gwaves/duduclock/src/task.cpp

#include <TaskScheduler.h>
#include "tftUtil.h"
#include "net.h"
#include "common.h"
#include <dht11.h> //temp sensor

dht11 DHT;
#define DHT11_PIN 6  

enum CurrentPage currentPage = SETTING;
String scrollText[5]; // 轮播天气的信息
int currentIndex = 0; // 轮播索引
int currnetImgAnimIndex = 0; // 太空人动画索引
int tipsIndex = 0; // 获取数据时，动态文字的索引
volatile bool gTipsNeedUpdate = false; // 定时器中断标志，提示需要更新
NowWeather nowWeather; // 记录查询到的实况天气数据
FutureWeather futureWeather; // 记录查询到的七日天气数据
unsigned int timerCount = 0; // 计数器的值(ms)
bool isScrolling = false; // 轮播文字动画是否进行中
int scrollAnimPos = 0; // 轮播文字动画当前位置
String scrollAnimText = ""; // 当前轮播的文字

void drawWeatherContent();
void drawFutureWeatherPage();
void doScrollTextData(String win, int air, String text, String feelsLike, String vis);
void drawWeaImage(int icon);
void drawFutureWeaImage(int wea_img, int x, int y);
void drawCityAir(String city,int air);
void drawTHProgressBar(int temperature, int humidity);
void drawDateWeek();
void drawTitle();
void drawNumsByCount(unsigned int count);
String getWea(int icon);
String week(int tm_wday);
String monthDay(int tm_mon, int tm_mday);
void doHourMinuteSecond(int hour,int minute,int second,int *hourH,int *hourL,int *minuteH,int *minuteL,int *secondH,int *secondL);


//////////////////////////////// 多任务区域/////////////////////////////
void tAnimCallback();
void tScrollTextCallback();
void tScrollAnimCallback();
void tQueryWeatherCallback();
void tQueryFutureWeatherCallback();
void tCheckWiFiCallback();
void tCheckTimeCallback();
void tGetLocalTempCallback();
Scheduler runner;
Task tAnim(30, TASK_FOREVER, &tAnimCallback, &runner, true); // 30毫秒播放一帧太空人动画
Task tScrollText(5000, TASK_FOREVER, &tScrollTextCallback, &runner, true); // 5秒触发一次轮播
Task tScrollAnim(30, TASK_FOREVER, &tScrollAnimCallback, &runner, false); // 30毫秒滚动一帧文字
Task tQueryWeather(8*60 * 60 * 1000, TASK_FOREVER, &tQueryWeatherCallback, &runner, false); // 8x60分钟查询一次实况天气情况
Task tQueryFutureWeather(24*60 * 60 * 1000, TASK_FOREVER, &tQueryFutureWeatherCallback, &runner, false); // 24小时查询一次一周天气情况
Task tCheckWiFi(5 * 60 * 1000, TASK_FOREVER, &tCheckWiFiCallback, &runner, true); // 5分钟检查一次网络状态
Task tCheckTime(58 * 60 * 1000, TASK_FOREVER, &tCheckTimeCallback, &runner, true); // 58分钟进行一次NTP对时
Task tGetLocalTemp(30*1000,TASK_FOREVER,&tGetLocalTempCallback,&runner,true); //每隔30秒读一次本地温湿度
// 启动runner
void startRunner(){
  runner.startNow();
}
// 执行runner
void executeRunner(){
  runner.execute();
}
// 切换到非实况天气页面时，失能太空人动画和轮播天气情况的线程
void disableAnimScrollText(){
  tAnim.disable();
  tScrollText.disable();
}
// 切换回实况天气页面时，再开启太空人动画和轮播天气情况的线程
void enableAnimScrollText(){
  tAnim.enable();
  tScrollText.enable();
}
////////////////////////////////////////////////////////////////////////


//////////////// 定时器相关区域//////////////////////////////////////////
// 定义定时器
hw_timer_t *timerQueryWeather = NULL;
hw_timer_t *timerShowTips = NULL;
void IRAM_ATTR onTimerQueryWeather() {
  // 使能查询天气的多线程任务
  tQueryWeather.enable();
  tQueryFutureWeather.enable();
} 
void IRAM_ATTR onTimerShowTips() {
  // 中断中只做最小操作，UI绘制移到主循环
  tipsIndex++;
  if(tipsIndex == 6){
    tipsIndex = 0;
  }
  gTipsNeedUpdate = true;
}

// 在主循环或轮询中调用，实际执行UI绘制
void drawTipsIfNeeded(){
  if(!gTipsNeedUpdate) return;
  gTipsNeedUpdate = false;
  if(tipsIndex == 0){
    draw2LineText("同步天气数据",".");
  }else if(tipsIndex == 1){
    draw2LineText("同步天气数据","..");
  }else if(tipsIndex == 2){
    draw2LineText("同步天气数据","...");
  }else if(tipsIndex == 3){
    draw2LineText("同步天气数据","....");
  }else if(tipsIndex == 4){
    draw2LineText("同步天气数据",".....");
  }else if(tipsIndex == 5){
    draw2LineText("同步天气数据","......");
  }
}
// 初始化定时器，让查询天气的多线程任务在一小时后再使能
void startTimerQueryWeather(){
  timerQueryWeather = timerBegin(0, 80, true);// 1us计数一次
  timerAttachInterrupt(timerQueryWeather, &onTimerQueryWeather, false);
  timerAlarmWrite(timerQueryWeather, 3600000000, false); // 执行完一次后就取消这个定时器 (3600000000)3600秒，即60分钟后使能
  timerAlarmEnable(timerQueryWeather); 
}
// 初始化定时器，在获取初始数据时，给用户提示
void startTimerShowTips(){
  timerShowTips = timerBegin(1, 80, true);// 1us计数一次
  timerAttachInterrupt(timerShowTips, &onTimerShowTips, false); 
  timerAlarmWrite(timerShowTips, 1000000, true); // 每秒执行一次
  timerAlarmEnable(timerShowTips); 
}
///////////////////////////////////////////////////////////////////////


/////////// 绘制整个页面区域////////////////////////////////////////////
// 绘制一周天气页面
void drawFutureWeatherPage(){
  reflashTFT(); // 清空屏幕
  // 绘制标题
  clk.createSprite(240, 60);
  clk.loadFont(clock_other_title_35);
  clk.setTextDatum(CC_DATUM);
  clk.setTextColor(penColor);
  clk.fillSprite(backFillColor);  
  clk.drawString("6日天气预报",120,30);
  clk.drawFastHLine(0,56,240,penColor);
  clk.drawFastHLine(0,58,240,penColor);
  clk.pushSprite(0,0);
  clk.deleteSprite();
  // 绘制天气图案
  drawFutureWeaImage(futureWeather.day1wea_img, 15, 65);
  drawFutureWeaImage(futureWeather.day2wea_img, 95, 65);
  drawFutureWeaImage(futureWeather.day3wea_img, 175, 65);
  drawFutureWeaImage(futureWeather.day4wea_img, 15, 195);
  drawFutureWeaImage(futureWeather.day5wea_img, 95, 195);
  drawFutureWeaImage(futureWeather.day6wea_img, 175, 195);
  // 绘制上部分文字
  clk.loadFont(clock_future_weather_20);
  clk.setTextDatum(CC_DATUM);
  clk.createSprite(240, 70);
  clk.setTextColor(penColor);
  clk.fillSprite(backFillColor);
  clk.drawString(futureWeather.day1date.substring(5),40,10);
  clk.drawString(futureWeather.day1wea,40,35);
  clk.drawString(String(futureWeather.day1tem_night) + "-" + String(futureWeather.day1tem_day) + "℃",40,60);
  clk.drawString(futureWeather.day2date.substring(5),120,10);
  clk.drawString(futureWeather.day2wea,120,35);
  clk.drawString(String(futureWeather.day2tem_night) + "-" + String(futureWeather.day2tem_day) + "℃",120,60);
  clk.drawString(futureWeather.day3date.substring(5),200,10);
  clk.drawString(futureWeather.day3wea,200,35);
  clk.drawString(String(futureWeather.day3tem_night) + "-" + String(futureWeather.day3tem_day) + "℃",200,60);
  clk.pushSprite(0,115);
  clk.deleteSprite();
  // 绘制下部分文字
  clk.createSprite(240, 70);
  clk.setTextColor(penColor);
  clk.fillSprite(backFillColor);
  clk.drawString(futureWeather.day4date.substring(5),40,10);
  clk.drawString(futureWeather.day4wea,40,35);
  clk.drawString(String(futureWeather.day4tem_night) + "-" + String(futureWeather.day4tem_day) + "℃",40,60);
  clk.drawString(futureWeather.day5date.substring(5),120,10);
  clk.drawString(futureWeather.day5wea,120,35);
  clk.drawString(String(futureWeather.day5tem_night) + "-" + String(futureWeather.day5tem_day) + "℃",120,60);
  clk.drawString(futureWeather.day6date.substring(5),200,10);
  clk.drawString(futureWeather.day6wea,200,35);
  clk.drawString(String(futureWeather.day6tem_night) + "-" + String(futureWeather.day6tem_day) + "℃",200,60);
  clk.pushSprite(0,245);
  clk.deleteSprite();
  clk.unloadFont();
}
// 绘制空气质量页面
void drawAirPage(){
  reflashTFT(); // 清空屏幕
  clk.loadFont(air_24);
  // 绘制标题
  clk.createSprite(240, 50);
  clk.fillSprite(backFillColor);
  clk.setTextDatum(CC_DATUM);
  clk.setTextColor(penColor);
  clk.drawString("空气质量指数",120,25);
  clk.pushSprite(0,0);
  clk.deleteSprite();
  // 绘制六种污染物
  clk.setTextDatum(ML_DATUM);
  clk.setTextColor(TFT_WHITE);
  // pm10 颗粒物
  clk.createSprite(236, 43);
  clk.fillSprite(backFillColor);
  clk.fillRoundRect(0,0,236,43,7,TFT_DARKGREY);
  clk.drawString("颗粒物",10,23);
  clk.drawString("PM10",110,23);
  clk.drawString(nowWeather.pm10,185,23);
  clk.pushSprite(2,50);
  clk.deleteSprite();
  // pm2p5 颗粒物
  clk.createSprite(236, 43);
  clk.fillSprite(backFillColor);
  clk.fillRoundRect(0,0,236,43,7,0x2C3E);
  clk.drawString("颗粒物",10,23);
  clk.drawString("PM2.5",110,23);
  clk.drawString(nowWeather.pm2p5,185,23);
  clk.pushSprite(2,95);
  clk.deleteSprite();
  // no2  二氧化氮
  clk.createSprite(236, 43);
  clk.fillSprite(backFillColor);
  clk.fillRoundRect(0,0,236,43,7,0x0E27);
  clk.drawString("二氧化氮",10,23);
  clk.drawString("NO2",110,23);
  clk.drawString(nowWeather.no2,185,23);
  clk.pushSprite(2,140);
  clk.deleteSprite();
  // so2  二氧化硫
  clk.createSprite(236, 43);
  clk.fillSprite(backFillColor);
  clk.fillRoundRect(0,0,236,43,7,TFT_GOLD);
  clk.drawString("二氧化硫",10,23);
  clk.drawString("SO2",110,23);
  clk.drawString(nowWeather.so2,185,23);
  clk.pushSprite(2,185);
  clk.deleteSprite();
  // co  一氧化碳
  clk.createSprite(236, 43);
  clk.fillSprite(backFillColor);
  clk.fillRoundRect(0,0,236,43,7,TFT_ORANGE);
  clk.drawString("一氧化碳",10,23);
  clk.drawString("CO",110,23);
  clk.drawString(nowWeather.co,185,23);
  clk.pushSprite(2,230);
  clk.deleteSprite();
  // o3  臭氧
  clk.createSprite(236, 43);
  clk.fillSprite(backFillColor);
  clk.fillRoundRect(0,0,236,43,7,TFT_RED);
  clk.drawString("臭氧",10,23);
  clk.drawString("O3",110,23);
  clk.drawString(nowWeather.o3,185,23);
  clk.pushSprite(2,275);
  clk.deleteSprite();
  clk.unloadFont();
}
// 绘制实况天气页面
void drawWeatherPage(){
  //清空屏幕
  reflashTFT();
  //绘制标题
  drawTitle();
  //绘制时间、日期、星期
  drawDateWeek();
  //绘制温湿度图标
  if(backColor == BACK_BLACK){
    tft.pushImage(7,235,40,40,temperature_black);
    tft.pushImage(5,275,40,40,humidity_black);
  }else{
    tft.pushImage(7,235,40,40,temperature);
    tft.pushImage(5,275,40,40,humidity);
  } 
  // 绘制天气相关内容
  drawWeatherContent();
}
// 绘制计时器页面
void drawTimerPage(){
  //清空屏幕
  reflashTFT();
  //绘制标题
  clk.createSprite(240, 60);
  clk.loadFont(clock_other_title_35);
  clk.setTextDatum(CC_DATUM);
  clk.setTextColor(penColor);
  clk.fillSprite(backFillColor);  
  clk.drawString("计时器",120,30);
  clk.drawFastHLine(0,56,240,penColor);
  clk.drawFastHLine(0,58,240,penColor);
  clk.pushSprite(0,0);
  clk.deleteSprite();
  //显示提示文字
  clk.setColorDepth(8);
  clk.setTextDatum(CC_DATUM);
  clk.loadFont(clock_timer_24);
  clk.createSprite(240, 60);
  clk.setTextColor(penColor);
  clk.fillSprite(backFillColor);
  clk.drawString("单击开启/停止计时",120,45);
  clk.drawString("长按3秒计数器归零",120,15);
  clk.pushSprite(0,250);
  clk.deleteSprite();
  clk.unloadFont(); 
  //根据计数器当前的数值进行绘制
  drawNumsByCount(timerCount);
}

// 绘制出厂设置页面
void drawResetPage(){
  //清空屏幕
  reflashTFT();
  // 绘制标题
  clk.createSprite(240, 60);
  clk.loadFont(clock_other_title_35);
  clk.setTextDatum(CC_DATUM);
  clk.setTextColor(penColor);
  clk.fillSprite(backFillColor);  
  clk.drawString("还原设置",120,30);
  clk.drawFastHLine(0,56,240,penColor);
  clk.drawFastHLine(0,58,240,penColor);
  clk.pushSprite(0,0);
  clk.deleteSprite();
  // 绘制提示文字
  clk.createSprite(240, 260);
  clk.loadFont(clock_tips_28);
  clk.setTextDatum(CC_DATUM);
  clk.setTextColor(penColor);
  clk.fillSprite(backFillColor);  
  clk.drawString("长按3秒钟",120,90);
  clk.drawString("恢复出厂设置",120,140);
  clk.pushSprite(0,60);
  clk.deleteSprite();
}
// 绘制主题设置页面
void drawThemePage(){
  // 清空屏幕
  reflashTFT();
  // 绘制标题
  clk.createSprite(240, 60);
  clk.loadFont(clock_other_title_35);
  clk.setTextDatum(CC_DATUM);
  clk.setTextColor(penColor);
  clk.fillSprite(backFillColor);
  clk.drawString("主题切换",120,30);
  clk.drawFastHLine(0,56,240,penColor);
  clk.drawFastHLine(0,58,240,penColor);
  clk.pushSprite(0,0);
  clk.deleteSprite();
  // 绘制提示文字
  clk.createSprite(240, 260);
  clk.loadFont(clock_tips_28);
  clk.setTextDatum(CC_DATUM);
  clk.setTextColor(penColor);
  clk.fillSprite(backFillColor);  
  clk.drawString("长按3秒钟",120,90);
  if(backColor == BACK_BLACK){
    clk.drawString("切换白色主题",120,140);
  }else{
    clk.drawString("切换黑色主题",120,140);
  }
  clk.pushSprite(0,60);
  clk.deleteSprite();
}
/////////////////////////////////////////////////////////////////////


/////////// 多任务协程回调区域 ////////////////////////////////////////
// NTP对时
void tCheckTimeCallback(){
  getNTPTime();
}
// 检查Wifi状态,如果失败，重新连接
void tCheckWiFiCallback(){
  log_i("开始检查网络状态");
  checkWiFiStatus();
}
// 绘制太空人任务
void tAnimCallback(){
  int x=170, y=240 , w=70;
  if(backColor == BACK_BLACK){
    switch(currnetImgAnimIndex){
      case 0:
        tft.pushImage(x, y, w, w,yuhangyuan0_black);
        break;
      case 1:
        tft.pushImage(x, y, w, w,yuhangyuan1_black);
        break;
      case 2:
        tft.pushImage(x, y, w, w,yuhangyuan2_black);
        break;
      case 3:
        tft.pushImage(x, y, w, w,yuhangyuan3_black);
        break;
      case 4:
        tft.pushImage(x, y, w, w,yuhangyuan4_black);
        break;
      case 5:
        tft.pushImage(x, y, w, w,yuhangyuan5_black);
        break;
      case 6:
        tft.pushImage(x, y, w, w,yuhangyuan6_black);
        break;
      case 7:
        tft.pushImage(x, y, w, w,yuhangyuan7_black);
        break;
      case 8:
        tft.pushImage(x, y, w, w,yuhangyuan8_black);
        break;
      case 9:
        tft.pushImage(x, y, w, w,yuhangyuan9_black);
        break;
      default:
        currnetImgAnimIndex = 9;
        break;
    }
  }else{
    switch(currnetImgAnimIndex){
      case 0:
        tft.pushImage(x, y, w, w,yuhangyuan0);
        break;
      case 1:
        tft.pushImage(x, y, w, w,yuhangyuan1);
        break;
      case 2:
        tft.pushImage(x, y, w, w,yuhangyuan2);
        break;
      case 3:
        tft.pushImage(x, y, w, w,yuhangyuan3);
        break;
      case 4:
        tft.pushImage(x, y, w, w,yuhangyuan4);
        break;
      case 5:
        tft.pushImage(x, y, w, w,yuhangyuan5);
        break;
      case 6:
        tft.pushImage(x, y, w, w,yuhangyuan6);
        break;
      case 7:
        tft.pushImage(x, y, w, w,yuhangyuan7);
        break;
      case 8:
        tft.pushImage(x, y, w, w,yuhangyuan8);
        break;
      case 9:
        tft.pushImage(x, y, w, w,yuhangyuan9);
        break;
      default:
        currnetImgAnimIndex = 9;
        break;
    }
  }
  currnetImgAnimIndex += 1;
  if(currnetImgAnimIndex == 10){
    currnetImgAnimIndex = 0;
  } 
}
// 轮播ScrollText任务（触发器，每5秒启动一次动画）
void tScrollTextCallback(){
  if(!isScrolling && scrollText[currentIndex]){
    isScrolling = true;
    scrollAnimPos = 24;
    scrollAnimText = scrollText[currentIndex];
    tScrollAnim.enable();
  }
}

// 轮播文字逐帧动画
void tScrollAnimCallback(){
  if(!isScrolling) return;

  clk.setColorDepth(8);
  clk.loadFont(city_wea_24);
  clk.createSprite(160, 24);
  clk.setTextColor(penColor);
  clk.fillSprite(backFillColor);
  clk.setTextDatum(CC_DATUM);
  clk.drawString(scrollAnimText, 80, scrollAnimPos + 12);
  clk.pushSprite(5, 102);
  clk.deleteSprite();
  clk.unloadFont();

  scrollAnimPos--;
  if(scrollAnimPos <= 0){
    isScrolling = false;
    tScrollAnim.disable();
    if(currentIndex >= 4){
      currentIndex = 0;
    }else{
      currentIndex++;
    }
  }
}
// 查询天气和空气质量
void tQueryWeatherCallback(){
  getNowWeather();
  getAir();
  if(queryNowWeatherSuccess || queryAirSuccess){
    Serial.println("更新实时天气信息");
    // 如果是在实况天气页面，则绘制天气相关内容
    if(currentPage == WEATHER){
      drawWeatherContent();
    }
  }
}
// 查询未来天气
void tQueryFutureWeatherCallback(){
  getFutureWeather();
  if(queryFutureWeatherSuccess){ // 查询一周天气成功，再继续下面的操作
    Serial.println("更新一周天气信息");
    // 如果是在一周天气页面，则绘制一周天气相关内容
    if(currentPage == FUTUREWEATHER){
      drawFutureWeatherPage();
    }
  }
}
/////////////////////////////////////////////////////////////////////


// 根据计数器当前的数值进行绘制
void drawNumsByCount(unsigned int count){
  clk.setColorDepth(8);
  clk.setTextDatum(CC_DATUM);
  clk.createSprite(240, 180);
  clk.setTextColor(penColor);
  clk.fillSprite(backFillColor);
  // 根据 count 计数器的毫秒值，计算对应的小时、分、秒、毫秒 
  int hour = count / 1000 / 60 / 60;
  int minute = (count / 1000 / 60) % 60;
  int second = (count / 1000) % 60;
  int millisecond = count % 1000;
  clk.loadFont(clock_timer_hour_52);
  clk.setTextColor(penColor);
  clk.drawString(String(hour) + " H",120,50);
  clk.unloadFont(); 
  clk.loadFont(clock_num_big_64);
  clk.drawString(String(minute / 10),20,120);
  clk.drawString(String(minute % 10),55,120);
  clk.drawString(":",80,120);
  clk.setTextColor(0xFC60);
  clk.drawString(String(second / 10),110,120);
  clk.drawString(String(second % 10),145,120);
  clk.unloadFont();
  clk.loadFont(clock_num_50);
  clk.setTextColor(TFT_RED);
  clk.drawString(String((millisecond / 10) / 10),187,123);
  clk.drawString(String((millisecond / 10) % 10),215,123);
  clk.unloadFont();
  // Serial.print(String(millisecond));Serial.println("毫秒");
  // Serial.print(String(second));Serial.println("秒");
  // Serial.print(String(minute));Serial.println("分");
  // Serial.print(String(hour));Serial.println("时");
  clk.pushSprite(0,70);
  clk.deleteSprite();
}
// 绘制天气相关内容
void drawWeatherContent(){
  //绘制温湿度条（内部已处理清屏，避免数字变化残影）
  drawTHProgressBar(nowWeather.temp,nowWeather.humidity);
  //绘制城市、空气质量
  drawCityAir(city,nowWeather.air);
  //绘制天气图案和文字
  drawWeaImage(nowWeather.icon);
  //处理轮播字条数据(风向win,空气指数air,天气实况text,体感温度feelsLike,能见度vis)
  doScrollTextData(nowWeather.win, nowWeather.air, nowWeather.text, nowWeather.feelsLike, nowWeather.vis);
}
//处理轮播字条数据(风向win,空气指数air,天气实况text,体感温度feelsLike,能见度vis)
void doScrollTextData(String win, int air, String text, String feelsLike, String vis){
  scrollText[0] = "";
  scrollText[1] = "";
  scrollText[2] = "";
  scrollText[3] = "";
  scrollText[4] = "";
  scrollText[0] = "今日" + text;
  scrollText[1] = win;
  scrollText[2] = feelsLike;
  scrollText[3] = vis;
  scrollText[4] += "空气指数";
  scrollText[4] += air;
}
//绘制天气图案和文字
void drawWeaImage(int icon){
  String s = getWea(icon);
  if(backColor == BACK_BLACK){
    if(s.equals("雪")){
      tft.pushImage(180,55,50,50,xue_black);
    }else if(s.equals("雷")){
      tft.pushImage(180,55,50,50,lei_black);
    }else if(s.equals("沙尘")){
      tft.pushImage(180,55,50,50,shachen_black);
    }else if(s.equals("雾")){
      tft.pushImage(180,55,50,50,wu_black);
    }else if(s.equals("冰雹")){
      tft.pushImage(180,55,50,50,bingbao_black);
    }else if(s.equals("多云")){
      tft.pushImage(180,55,50,50,yun_black);
    }else if(s.equals("雨")){
      tft.pushImage(180,55,50,50,yu_black);
    }else if(s.equals("阴")){
      tft.pushImage(180,55,50,50,yin_black);
    }else if(s.equals("晴")){
      tft.pushImage(180,55,50,50,qing_black);
    }
  }else{
    if(s.equals("雪")){
      tft.pushImage(180,55,50,50,xue);
    }else if(s.equals("雷")){
      tft.pushImage(180,55,50,50,lei);
    }else if(s.equals("沙尘")){
      tft.pushImage(180,55,50,50,shachen);
    }else if(s.equals("雾")){
      tft.pushImage(180,55,50,50,wu);
    }else if(s.equals("冰雹")){
      tft.pushImage(180,55,50,50,bingbao);
    }else if(s.equals("多云")){
      tft.pushImage(180,55,50,50,yun);
    }else if(s.equals("雨")){
      tft.pushImage(180,55,50,50,yu);
    }else if(s.equals("阴")){
      tft.pushImage(180,55,50,50,yin);
    }else if(s.equals("晴")){
      tft.pushImage(180,55,50,50,qing);
    }
  }
  clk.setColorDepth(8);
  clk.setTextDatum(CC_DATUM);
  clk.loadFont(city_wea_24);
  clk.createSprite(60, 28);
  clk.fillSprite(backFillColor);
  clk.fillRoundRect(0,0,60,32,0,0x4208);// 进度条填充(x方向,y方向,长度,高度,圆角,颜色)
  clk.setTextColor(0xFFFF);
  clk.drawString(s,29,15);
  clk.pushSprite(172,120);
  clk.deleteSprite();
  clk.unloadFont(); 
}
//绘制一周天气图案
void drawFutureWeaImage(int wea_img, int x, int y){
  String s = getWea(wea_img);
  if(backColor == BACK_BLACK){
    if(s.equals("雪")){
      tft.pushImage(x,y,50,50,xue_black);
    }else if(s.equals("雷")){
      tft.pushImage(x,y,50,50,lei_black);
    }else if(s.equals("沙尘")){
      tft.pushImage(x,y,50,50,shachen_black);
    }else if(s.equals("雾")){
      tft.pushImage(x,y,50,50,wu_black);
    }else if(s.equals("冰雹")){
      tft.pushImage(x,y,50,50,bingbao_black);
    }else if(s.equals("多云")){
      tft.pushImage(x,y,50,50,yun_black);
    }else if(s.equals("雨")){
      tft.pushImage(x,y,50,50,yu_black);
    }else if(s.equals("阴")){
      tft.pushImage(x,y,50,50,yin_black);
    }else if(s.equals("晴")){
      tft.pushImage(x,y,50,50,qing_black);
    }
  }else{
    if(s.equals("雪")){
      tft.pushImage(x,y,50,50,xue);
    }else if(s.equals("雷")){
      tft.pushImage(x,y,50,50,lei);
    }else if(s.equals("沙尘")){
      tft.pushImage(x,y,50,50,shachen);
    }else if(s.equals("雾")){
      tft.pushImage(x,y,50,50,wu);
    }else if(s.equals("冰雹")){
      tft.pushImage(x,y,50,50,bingbao);
    }else if(s.equals("多云")){
      tft.pushImage(x,y,50,50,yun);
    }else if(s.equals("雨")){
      tft.pushImage(x,y,50,50,yu);
    }else if(s.equals("阴")){
      tft.pushImage(x,y,50,50,yin);
    }else if(s.equals("晴")){
      tft.pushImage(x,y,50,50,qing);
    }
  } 
}
//绘制城市、空气质量
void drawCityAir(String city,int air){
  clk.setColorDepth(8);
  clk.setTextDatum(CC_DATUM);
  //城市
  clk.loadFont(city_wea_24);
  clk.createSprite(100, 32);
  clk.fillSprite(backFillColor);
  clk.setTextColor(0xFC60);
  clk.drawString(city,50,17); 
  clk.pushSprite(0,60);
  clk.deleteSprite();
  clk.unloadFont();
  //空气质量， ≤50优（绿色），≤100良（蓝），≤150中（橙），≤200差（红）
  clk.loadFont(city_wea_24);
  String level;
  uint16_t color;
  if(air <= 50){
    color = 0x0E27;
    level = "优";
  }else if(air <= 100){
    color = 0x2C3E;
    level = "良";
  }else if(air <= 150){
    color = 0xFC60;
    level = "中";
  }else{
    color = TFT_RED;
    level = "差";
  }
  clk.createSprite(60, 32);
  clk.fillSprite(backFillColor);
  clk.fillRoundRect(0,0,60,32,7,color);// 进度条填充(x方向,y方向,长度,高度,圆角,颜色)
  clk.setTextColor(0xFFFF);
  clk.drawString(level,30,17);
  clk.pushSprite(105,60);
  clk.deleteSprite();
  clk.unloadFont();
}
// 绘制温湿度数据
void drawTHProgressBar(int temperature, int humidity){
  // 清除整个温湿度文字区域（左右两侧），防止数字位数或正负号变化时产生残影
  tft.fillRect(28, 238, 142, 58, backFillColor);
  tft.loadFont(city_wea_24);
  tft.setTextColor(penColor,backFillColor);
  if(temperature < 0){
    tft.drawNumber(temperature,115,245);
  }else{
    tft.drawNumber(temperature,127,245);
  }
  tft.drawString("℃",149,245);
  if(humidity >= 100){
    tft.drawNumber(humidity,115,285);
  }else{
    tft.drawNumber(humidity,127,285);
  }
  tft.drawString("%",157,285);

  //绘制室内温度信息
  tft.setTextColor(penColor,backFillColor);
  if(DHT.temperature < 0){
    tft.drawNumber(DHT.temperature,35,245);
  }else{
    tft.drawNumber(DHT.temperature,57,245);
  }
  tft.drawString("℃",79,245);
  if(DHT.humidity >= 100){
    tft.drawNumber(DHT.humidity,35,285);
  }else{
    tft.drawNumber(DHT.humidity,57,285);
  }
  tft.drawString("%",87,285);

  tft.unloadFont();
}
// 绘制时间、日期、星期
void drawDateWeek(){
  // 获取RTC时间
  struct tm timeinfo;
  if (!getLocalTime(&timeinfo)){
    Serial.println("获取RTC时间失败");
    return;
  }
  clk.setColorDepth(8);
  //中部时、分、秒
  int hourH,hourL,minuteH,minuteL,secondH,secondL;
  doHourMinuteSecond(timeinfo.tm_hour,timeinfo.tm_min,timeinfo.tm_sec,&hourH,&hourL,&minuteH,&minuteL,&secondH,&secondL);
  //时、分
  clk.createSprite(165, 60);
  clk.setTextColor(penColor);
  clk.fillSprite(backFillColor);
  clk.loadFont(clock_num_big_64);
  clk.setTextDatum(CC_DATUM);
  clk.drawNumber(hourH,20,32);
  clk.drawNumber(hourL,55,32);
  clk.drawString(":",80,32);
  clk.setTextColor(0xFC60);
  clk.drawNumber(minuteH,110,32);
  clk.drawNumber(minuteL,145,32);
  clk.unloadFont();
  clk.pushSprite(5,135);
  clk.deleteSprite();
  //秒
  clk.createSprite(55, 40);
  clk.fillSprite(backFillColor);
  clk.loadFont(clock_num_mid_35);
  clk.setTextDatum(CC_DATUM);
  clk.setTextColor(TFT_RED);
  clk.drawNumber(secondH,12,20);
  clk.drawNumber(secondL,32,20);
  clk.unloadFont();
  clk.pushSprite(180,155);
  clk.deleteSprite();
  //底部日期、星期
  clk.loadFont(city_wea_24);
  //星期
  clk.createSprite(58, 25);
  clk.setTextColor(penColor);
  clk.fillSprite(backFillColor);
  clk.setTextDatum(CC_DATUM);  
  clk.drawString(week(timeinfo.tm_wday),27,16);
  clk.pushSprite(123,202);
  clk.deleteSprite();
  //月日
  clk.createSprite(98, 25);
  clk.setTextColor(penColor);
  clk.fillSprite(backFillColor);
  clk.setTextDatum(CC_DATUM);
  clk.drawString(monthDay(timeinfo.tm_mon,timeinfo.tm_mday),49,16);
  clk.pushSprite(5,202);
  clk.deleteSprite();
  clk.unloadFont();
}
// 绘制标题
void drawTitle(){
  clk.createSprite(240, 51);
  clk.setTextColor(penColor);
  clk.fillSprite(backFillColor);
  //clk.loadFont(name_42);
  clk.loadFont(city_wea_24);
  clk.setTextDatum(CC_DATUM);
  //clk.drawString("Taotao Clock",120,35);
  clk.drawString("Make    KC    Great",120,35);
  clk.unloadFont();
  clk.drawFastHLine(0,48,240,penColor);
  clk.drawFastHLine(0,50,240,penColor);
  clk.pushSprite(0,0);
  clk.deleteSprite();
}
// 根据icon获得天气状况
String getWea(int icon){
  String s = "";
  switch (icon){
    case 100:
    case 150:
      s = "晴";
      break;
    case 104:
      s = "阴";
      break;
    case 300:
    case 301:
    case 305:
    case 306:
    case 307:
    case 308:
    case 309:
    case 310:
    case 311:
    case 312:
    case 313:
    case 314:
    case 315:
    case 316:
    case 317:
    case 318:
    case 350:
    case 351:
    case 399:
      s = "雨";
      break;
    case 101:
    case 102:
    case 103:
    case 151:
    case 152:
    case 153:
      s = "多云";
      break;
    case 304:
      s = "冰雹";
      break;
    case 500:
    case 501:
    case 502:
    case 509:
    case 510:
    case 511:
    case 512:
    case 513:
    case 514:
    case 515:
      s = "雾";
      break;
    case 503:
    case 504:
    case 507:
    case 508:
      s = "沙尘";
      break;
    case 302:
    case 303:
      s = "雷";
      break;
    case 400:
    case 401:
    case 402:
    case 403:
    case 404:
    case 405:
    case 406:
    case 407:
    case 408:
    case 409:
    case 410:
    case 456:
    case 457:
    case 499:
      s = "雪";
      break;
    default:
      s = "晴";
      break;  
  }
  return s;
}
//处理星期
String week(int tm_wday){
  String wk[7] = {"日","一","二","三","四","五","六"};
  String s = "周" + wk[tm_wday];
  return s;
}
//处理月日
String monthDay(int tm_mon, int tm_mday){
  String s = "";
  s = s + (tm_mon + 1);
  s = s + "月" + tm_mday + "日";
  return s;
}
//处理时分秒
void doHourMinuteSecond(int hour,int minute,int second,int *hourH,int *hourL,int *minuteH,int *minuteL,int *secondH,int *secondL){
  *hourH = hour / 10;
  *hourL = hour % 10;
  *minuteH = minute / 10;
  *minuteL = minute % 10;
  *secondH = second / 10;
  *secondL = second % 10;
}

void tGetLocalTempCallback()
{
  int chk;
  int errCnt=0;
  log_v("DHT11, \t");
  chk = DHT.read(DHT11_PIN);    // READ DATA
  while(chk != DHTLIB_OK && errCnt < 5){
    delay(100);
    chk = DHT.read(DHT11_PIN);    // READ DATA
    errCnt++;
  }
  switch (chk){
    case DHTLIB_OK:  
                log_v("OK,\t"); 
                break;
    case DHTLIB_ERROR_CHECKSUM: 
                log_e("DHT11 Checksum error"); 
                break;
    case DHTLIB_ERROR_TIMEOUT: 
                log_e("DHT11 Time out error"); 
                break;
    default: 
                log_e("DHT11 Unknown error"); 
                break;
  }
 // DISPLAT DATA
  log_v("%d \t %d",DHT.humidity,DHT.temperature);
  //只刷新温湿度区域，避免整屏闪烁
  if(currentPage == WEATHER){
    drawTHProgressBar(nowWeather.temp, nowWeather.humidity);
  }
}
