gwaves/duduclock/src/common.h

#ifndef __COMMON_H
#define __COMMON_H

#include <Arduino.h>
#include "img/yuhangyuan/yuhangyuan0_black.h"
#include "img/yuhangyuan/yuhangyuan1_black.h"
#include "img/yuhangyuan/yuhangyuan2_black.h"
#include "img/yuhangyuan/yuhangyuan3_black.h"
#include "img/yuhangyuan/yuhangyuan4_black.h"
#include "img/yuhangyuan/yuhangyuan5_black.h"
#include "img/yuhangyuan/yuhangyuan6_black.h"
#include "img/yuhangyuan/yuhangyuan7_black.h"
#include "img/yuhangyuan/yuhangyuan8_black.h"
#include "img/yuhangyuan/yuhangyuan9_black.h"
#include "img/yuhangyuan/yuhangyuan0.h"
#include "img/yuhangyuan/yuhangyuan1.h"
#include "img/yuhangyuan/yuhangyuan2.h"
#include "img/yuhangyuan/yuhangyuan3.h"
#include "img/yuhangyuan/yuhangyuan4.h"
#include "img/yuhangyuan/yuhangyuan5.h"
#include "img/yuhangyuan/yuhangyuan6.h"
#include "img/yuhangyuan/yuhangyuan7.h"
#include "img/yuhangyuan/yuhangyuan8.h"
#include "img/yuhangyuan/yuhangyuan9.h"
#include "img/wea/xue.h"
#include "img/wea/lei.h"
#include "img/wea/shachen.h"
#include "img/wea/wu.h"
#include "img/wea/bingbao.h"
#include "img/wea/yun.h"
#include "img/wea/yu.h"
#include "img/wea/yin.h"
#include "img/wea/qing.h"
#include "img/wea/xue_black.h"
#include "img/wea/lei_black.h"
#include "img/wea/shachen_black.h"
#include "img/wea/wu_black.h"
#include "img/wea/bingbao_black.h"
#include "img/wea/yun_black.h"
#include "img/wea/yu_black.h"
#include "img/wea/yin_black.h"
#include "img/wea/qing_black.h"
#include "img/temperature.h"
#include "img/humidity.h"
#include "img/temperature_black.h"
#include "img/humidity_black.h"
#include "img/QRcode.h"
#include "font/clock_num_big_64.h"
#include "font/clock_timer_hour_52.h"
#include "font/clock_num_mid_35.h"
#include "font/clock_num_50.h"
#include "font/city_wea_24.h"
#include "font/clock_tips_28.h"
#include "font/clock_timer_24.h"
#include "font/clock_future_weather_20.h"
#include "font/clock_other_title_35.h"
//#include "font/clock_title_45.h"
#include "font/air_24.h"
//#include "font/taotao_45.h"
#include "font/name_42.h"
#define NTP3 "ntp5.ntsc.ac.cn"
#define NTP2 "ntp5.ict.ac.cn"
#define NTP1 "ntp5.aliyun.com"
#define BACK_BLACK 0
#define BACK_WHITE 1
#define D4 12  // 开发板D4灯
#define BUTTON 8 // 按钮引脚
//#define KEY "7de934b2cca745c989f5cbedc4c0c195"  //test_tianqi key
#define KEY "20ba59bde7c149d88c3f6949f7770b98"  //pay money key
// 天气接口
const String cityURL = "https://geoapi.qweather.com/v2/city/lookup?key=";  //查询城市代码的接口
//以下地址为付费地址，每十次1分钱。
const String nowURL = "https://api.qweather.com/v7/weather/now?key="; // 实时天气接口
//const String futureURL = "https://api.qweather.com/v7/weather/3d?key="; // 3日天气预报接口
const String futureURL = "https://api.qweather.com/v7/weather/7d?key="; // 7日天气预报接口
const String airURL = "https://api.qweather.com/v7/air/now?key="; // 空气质量接口
const String myipURL = "http://ali.liutao1.com/get_ip"; // 获取本机IP地址
const String myIPGeoURL = "http://api.ipshudi.com/ipdata/?ip=";
const String myIPGeoURL2 = "&datatype=jsonp&token=4d3b6e67df0023fd5e1a588214be2ab7";//token

//以下地址为免费API地址，每天1000次请求
//const String nowURL = "https://devapi.qweather.com/v7/weather/now?key="; // 实时天气接口
//const String futureURL = "https://devapi.qweather.com/v7/weather/7d?key="; // 7日天气预报接口
//const String airURL = "https://devapi.qweather.com/v7/air/now?key="; // 空气质量接口
// 定义页面枚举 SETTING-配置页面  WEATHER-实况天气页面  FUTUREWEATHER-一周天气页面  TIMER-计时器  RESET-恢复出厂设置
enum CurrentPage{
  SETTING, WEATHER, AIR, FUTUREWEATHER, THEME, TIMER, ALARM, RESET
};
// 定义结构体
typedef struct {
  String text;
  int icon;
  int temp;
  String feelsLike;
  String win;
  String vis;
  int humidity;
  int air;
  String pm10;
  String pm2p5;
  String no2;
  String so2;
  String co;
  String o3;
} NowWeather;
typedef struct {
  String day0wea;
  int day0wea_img;
  String day0date;
  int day0tem_day;
  int day0tem_night;
  String day1wea;
  int day1wea_img;
  String day1date;
  int day1tem_day;
  int day1tem_night;
  String day2wea;
  int day2wea_img;
  String day2date;
  int day2tem_day;
  int day2tem_night;
  String day3wea;
  int day3wea_img;
  String day3date;
  int day3tem_day;
  int day3tem_night;
  String day4wea;
  int day4wea_img;
  String day4date;
  int day4tem_day;
  int day4tem_night;
  String day5wea;
  int day5wea_img;
  String day5date;
  int day5tem_day;
  int day5tem_night;
  String day6wea;
  int day6wea_img;
  String day6date;
  int day6tem_day;
  int day6tem_night;
} FutureWeather;
// 配置WiFi的网页代码
const String ROOT_HTML_PAGE1 PROGMEM = R"rawliteral(
  <!DOCTYPE html><html lang='zh'>
<head>
    <meta charset='UTF-8'>
    <meta name='viewport' content='width=device-width, initial-scale=1.0'>
    <link href='favicon.ico' rel='shortcut icon'>
    <title>TaoTao时钟配置页面</title>
    <style type='text/css'>
        #titleDiv{
            margin-top: 20px;
            height: 10%;
            width: 100%;
            text-align: center;
            font-size: 2rem;
            font-weight: bold;
        }
        .titleOption{
            text-align: center;
            margin-top: 30px;
            height: 40px;
            background-color: dodgerblue; 
            position: relative;
            color: #ffffff;
            border-radius: 5px;
            line-height: 40px;
        }
        #selectDiv {
            margin-top: 20px;
            height: 40px;
            border-radius: 5px;
            box-shadow: 0 0 5px #ccc;
            position: relative;   
        }
        select {
            border: none;
            outline: none;
            width: 100%;
            height: 40px;
            line-height: 40px;
            appearance: none;
            -webkit-appearance: none;
            -moz-appearance: none;
            text-align: center;
            font-size: 1rem;
        }
        .passAndCity{
            border: none;
            margin-top: 20px;
            height: 40px;
            border-radius: 5px;
            box-shadow: 0 0 5px #ccc;
            font-size: 1rem;
            position: relative;
            text-align: center;
        }
        #sub{
            text-align: center;
            margin-top: 50px;
            height: 40px;
            background-color: dodgerblue; 
            position: relative;
            color: #ffffff;
            border-radius: 5px;
            line-height: 40px;
            cursor: pointer;
        }
        #tail{
            font-size: 0.9rem;
            margin-top: 5px;
            width: 100%;
            text-align: center;
            color: #757575;
        }
    </style>
</head>
<body>
    <div id='titleDiv'>Taotao时钟2.0</div>
    <div id='tail'>gwaves工作室&nbsp&nbsp&nbsp&nbsp出品</div>
    <form action='configwifi' method='post' id='form' accept-charset="UTF-8">
        <div class='titleOption commonWidth'>WiFi名称</div>
        <div id='selectDiv' class='commonWidth'>
            <select name='ssid' id='ssid'>
                <option value=''></option>
)rawliteral";
const String ROOT_HTML_PAGE2 PROGMEM = R"rawliteral(
  </select>
        </div>
        <div class='titleOption commonWidth'>WiFi密码</div>
        <input type='text' placeholder='请输入WiFi密码' name='pass' id='pass' class='passAndCity commonWidth'>
        <div id='sub' onclick='doSubmit()'>提交</div>
    </form>
    <script type='text/javascript'>
        function doSubmit(){
            var select = document.getElementById('ssid');
            var selectValue = select.options[select.selectedIndex].value;
            if(selectValue == ''){
                alert('请选择要连接的WiFi');
                return;
            }
            if(document.getElementById('pass').value == ''){
                alert('请输入该WiFi的密码');
                return;
            }
            document.getElementById('form').submit();
        }
        var nodes = document.getElementsByClassName('commonWidth');
        var node = document.getElementById('sub');
        var screenWidth = window.screen.width;
        function setWidth(width){
            nodes[0].setAttribute('style',width);
            nodes[1].setAttribute('style',width);
            nodes[2].setAttribute('style',width);
            nodes[3].setAttribute('style',width);
            nodes[4].setAttribute('style',width);
            nodes[5].setAttribute('style',width);
            nodes[6].setAttribute('style',width);
            nodes[7].setAttribute('style',width);
        }
        if(screenWidth > 1000){
            setWidth('width: 40%;left: 30%;');
            node.setAttribute('style','width: 14%;left: 43%;');
        }else if(screenWidth > 800 && screenWidth <= 1000){
            setWidth('width: 50%;left: 25%;');
            node.setAttribute('style','width: 16%;left: 42%;');
        }else if(screenWidth > 600 && screenWidth <= 800){
            setWidth('width: 60%;left: 20%;');
            node.setAttribute('style','width: 20%;left: 40%;');
        }else if(screenWidth > 400 && screenWidth <= 600){
            setWidth('width: 74%;left: 13%;');
            node.setAttribute('style','width: 26%;left: 37%;');
        }else{
            setWidth('width: 90%;left: 5%;');
            node.setAttribute('style','width: 40%;left: 30%;');
        }
    </script>
</body>
</html>
)rawliteral";         

#endif
