gwaves/duduclock/src/task.h

#ifndef __TASK_H
#define __TASK_H

#include "common.h"
#include <esp32-hal-timer.h>
#include <WString.h>

void startTimerShowTips();
void startTimerQueryWeather();
extern String scrollText[5];
extern hw_timer_t *timerQueryWeather;
extern hw_timer_t *timerShowTips;
extern NowWeather nowWeather;
extern FutureWeather futureWeather;
extern enum CurrentPage currentPage;
extern unsigned int timerCount;
extern volatile bool gTipsNeedUpdate;
void drawTipsIfNeeded();
void drawWeatherContent();
void drawFutureWeatherPage();
void drawWeatherPage();
void drawTimerPage();
void drawAlarmPage();
void drawResetPage();
void drawThemePage();
void drawDateWeek();
void drawAirPage();
void drawNumsByCount(unsigned int count);
void startRunner();
void executeRunner();
void disableAnimScrollText();
void enableAnimScrollText();
void tGetLocalTempCallback();

#endif
