gwaves/duduclock/src/net.h

#ifndef __NET_H
#define __NET_H
#include "common.h"

void wifiConfigBySoftAP(void);
void doClient(void);
int connectDefaultWiFi(int timeOut_s);
void connectWiFi(int timeOut_s);
void getNowWeather(void);
void getFutureWeather(void);
void getAir(void);
void getNTPTime(void);
void getCityID(void);
void checkWiFiStatus(void);
void restartSystem(String msg, bool endTips);
int getMyGeo(void);
int getMyPubIP(void);
extern bool queryNowWeatherSuccess;
extern bool queryFutureWeatherSuccess;
extern bool queryAirSuccess;
extern String ssid;
extern String pass;
extern String city;
extern String adm;
extern String location;
extern bool isStartQuery;
extern String dft_wifi_exist;

#endif
