gwaves/duduclock/src/preferencesUtil.cpp

#include <Preferences.h>
#include "net.h"
#include "tftUtil.h"

Preferences prefs; // 声明Preferences对象

// 读取Wifi账号、密码和城市名称
void getWiFiCity(){
  prefs.begin("clock");
  ssid = prefs.getString("ssid", "");
  pass = prefs.getString("pass", "");
  //city = prefs.getString("city", "");
  //adm = prefs.getString("adm", "");
  location = prefs.getString("location", "");
  prefs.end();
}
void getNvsWifi(){
  prefs.begin("clock");
  ssid = prefs.getString("ssid", "");
  pass = prefs.getString("pass", "");
  prefs.end();
}
void setNvsDefaultWifiStat(){
  prefs.begin("clock");
  prefs.putString("dft_wifi_exist", dft_wifi_exist);
  prefs.end();
}
void getNvsDefaultWifiStat(){
  prefs.begin("clock");
  dft_wifi_exist = prefs.getString("dft_wifi_exist", "");
  prefs.end();
}
void setNvsWifi(){
  prefs.begin("clock");
  prefs.putString("ssid", ssid);
  prefs.putString("pass", pass);
  prefs.end();
}
// 写入Wifi账号、密码和城市名称
void setWiFiCity(){
  prefs.begin("clock");
  prefs.putString("ssid", ssid);
  prefs.putString("pass", pass);
  prefs.putString("city", city);
  prefs.putString("adm", adm);
  prefs.putString("location", location);
  prefs.end();
}
void setNvsCity(){
  prefs.begin("clock");
  prefs.putString("city", city);
  prefs.putString("adm", adm);
  prefs.putString("location", location);
  prefs.end();
}
void setNvsCityID(){
  prefs.begin("clock");
  prefs.putString("location", location);
  prefs.end();
}
void getNvsCityID(){
  prefs.begin("clock");
  location = prefs.getString("location", "");
  prefs.end();
}
void getNvsCity(){
  prefs.begin("clock");
  city = prefs.getString("city", "");
  adm = prefs.getString("adm", "");
  location = prefs.getString("location", "");
  prefs.end();
}
void clearNvsWifi(){
  prefs.begin("clock");
  prefs.remove("ssid");
  prefs.remove("pass");
  prefs.end();
}
// 清除Wifi账号、密码和城市相关信息
void clearWiFiCity(){
  prefs.begin("clock");
  prefs.remove("ssid");
  prefs.remove("pass");
  prefs.remove("city");
  prefs.remove("adm");
  prefs.remove("location");
  prefs.remove("backColor");
  prefs.remove("dft_wifi_exist");
  prefs.end();
}

// 获取屏幕背光颜色
void getBackColor(){
  prefs.begin("clock");
  backColor = prefs.getInt("backColor",BACK_WHITE);
  prefs.end();
}

// 设置屏幕背光颜色
void setBackColor(int backColor){
  prefs.begin("clock");
  prefs.putInt("backColor",backColor);
  prefs.end();
}

// 测试用，在读取NVS之前，先写入自己的Wifi信息，免得每次浪费时间再配网
void setInfo4Test(){
  prefs.begin("clock");
  prefs.putString("ssid", "tommy-home");
  prefs.putString("pass", "tommy-ssid");
  prefs.putString("city", "海淀");
  prefs.putString("adm", "北京市");
  prefs.putString("location", "101010200");
  prefs.end();
}
