gwaves/duduclock/src/preferencesUtil.h

#ifndef __PreferencesUtil_H
#define __PreferencesUtil_H

void getWiFiCity();
void setWiFiCity();
void clearWiFiCity();
void setInfo4Test();
void getBackColor();
void setBackColor(int backColor);
void getNvsCity();
void setNvsCity();
void setNvsWifi();
void getNvsWifi();
void setNvsCityID();
void getNvsCityID();
void clearNvsWifi();
void getNvsDefaultWifiStat();
void setNvsDefaultWifiStat();
#endif
